JakubKivi/Mini-Sumo/eagle/zapełniona.pdf

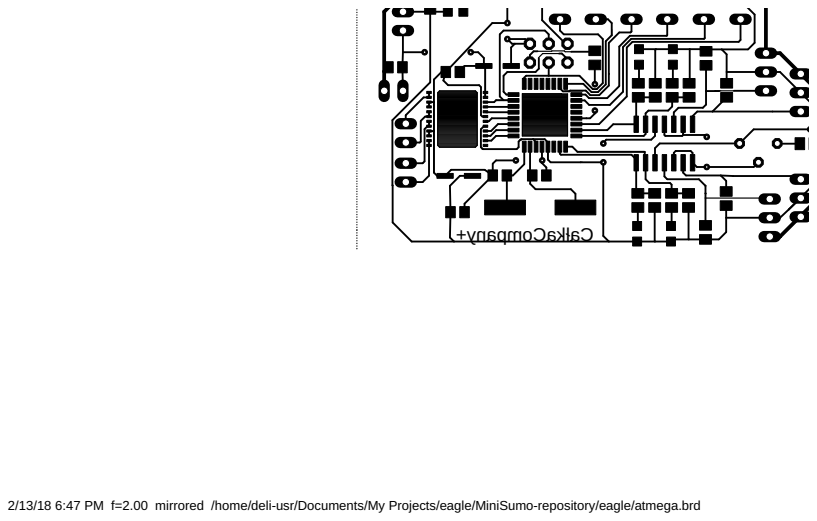
[picture p7: page 1]

2/13/18 6:47 PM f=2.00 mirrored /home/deli-usr/Documents/My Projects/eagle/MiniSumo-repository/eagle/atmega.brd
