JakubKivi/Mini-Sumo/eagle/zapełnionaBrzydka.pdf

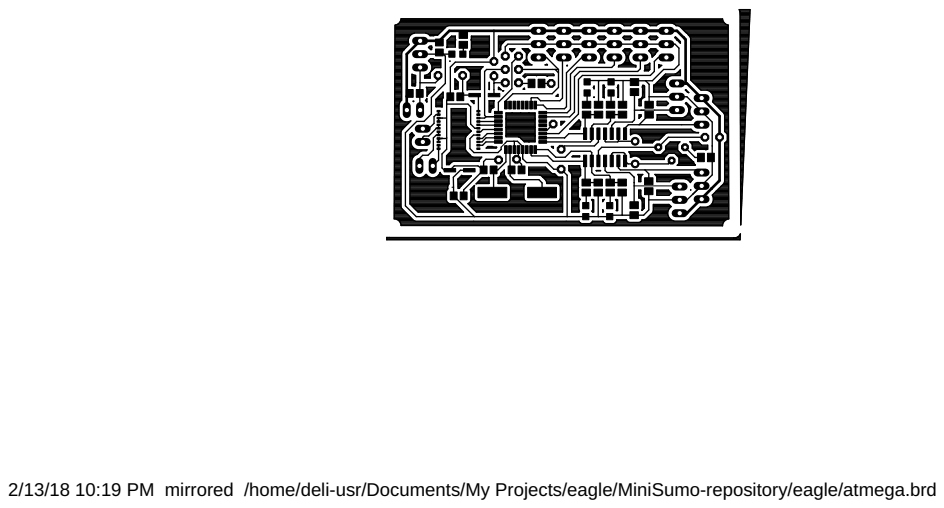
[picture p8: page 1]

2/13/18 10:19 PM mirrored /home/deli-usr/Documents/My Projects/eagle/MiniSumo-repository/eagle/atmega.brd
