JakubKivi/Mini-Sumo/eagle/zapełnionaBrzydka2.pdf

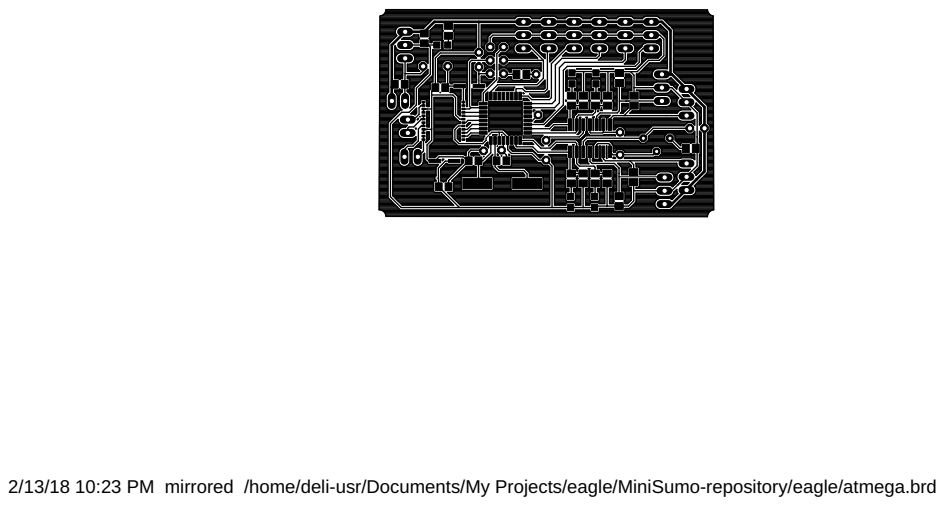
[picture p9: page 1]

2/13/18 10:23 PM mirrored /home/deli-usr/Documents/My Projects/eagle/MiniSumo-repository/eagle/atmega.brd
